KimJorgensen/KungFuFlash/firmware/d64.h

/*
 * Copyright (c) 2019-2023 Kim Jørgensen
 *
 * This software is provided 'as-is', without any express or implied
 * warranty.  In no event will the authors be held liable for any damages
 * arising from the use of this software.
 *
 * Permission is granted to anyone to use this software for any purpose,
 * including commercial applications, and to alter it and redistribute it
 * freely, subject to the following restrictions:
 *
 * 1. The origin of this software must not be misrepresented; you must not
 *    claim that you wrote the original software. If you use this software
 *    in a product, an acknowledgment in the product documentation would be
 *    appreciated but is not required.
 * 2. Altered source versions must be plainly marked as such, and must not be
 *    misrepresented as being the original software.
 * 3. This notice may not be removed or altered from any source distribution.
 *
 ******************************************************************************
 * Based on d642prg V2.09
 * Original source (C) Covert Bitops
 * (C)2003/2009 by iAN CooG/HokutoForce^TWT^HVSC
 */

#define D64_DOS_VERSION     0x41
#define D81_DOS_VERSION     0x44

#define D64_TRACKS          35
#define D71_TRACKS          70
#define D81_TRACKS          80
#define D81_SECTORS         40

#define D64_TRACK_DIR       18
#define D64_SECTOR_HEADER   0
#define D64_SECTOR_DIR      1
#define D81_TRACK_DIR       40
#define D81_SECTOR_DIR      3

#define D64_SECTOR_DATA_LEN 254
#define D64_SECTOR_LEN      256

static const u16 d64_track_offset[42] =
{
    0x0000, 0x0015, 0x002a, 0x003f, 0x0054, 0x0069, 0x007e, 0x0093,
    0x00a8, 0x00bd, 0x00d2, 0x00e7, 0x00fc, 0x0111, 0x0126, 0x013b,
    0x0150, 0x0165, 0x0178, 0x018b, 0x019e, 0x01b1, 0x01c4, 0x01d7,
    0x01ea, 0x01fc, 0x020e, 0x0220, 0x0232, 0x0244, 0x0256, 0x0267,
    0x0278, 0x0289, 0x029a, 0x02ab, 0x02bc, 0x02cd, 0x02de, 0x02ef,
    0x0300, 0x0311
};

static const char *d64_types[8] = {"DEL", "SEQ", "PRG", "USR", "REL", "CBM", "DIR", "???"};

typedef enum
{
  D64_TYPE_UNKNOWN = 0,
  D64_TYPE_D64,
  D64_TYPE_D71,
  D64_TYPE_D81
} D64_TYPE;

static u8 d64_get_type(FSIZE_t imgsize)
{
    switch (imgsize)
    {
        // D64
        case 174848:  // 35 tracks no errors
        case 175531:  // 35 w/ errors
        case 196608:  // 40 tracks no errors
        case 197376:  // 40 w/ errors
        case 205312:  // 42 tracks no errors
        case 206114:  // 42 w/ errors
            return D64_TYPE_D64;

        // D71
        case 349696:  // 70 tracks no errors
        case 351062:  // 70 w/ errors
            return D64_TYPE_D71;

        // D81
        case 819200:  // 80 tracks no errors
        case 822400:  // 80 w/ errors
            return D64_TYPE_D81;
    }

    return D64_TYPE_UNKNOWN;
}

typedef enum
{
  D64_FILE_DEL      = 0x00,
  D64_FILE_SEQ,
  D64_FILE_PRG,
  D64_FILE_USR,
  D64_FILE_REL,
  D64_FILE_CBM,
  D64_FILE_DIR,
  D64_FILE_LOCKED   = 0x40,
  D64_FILE_NO_SPLAT = 0x80
} D64_FILE_TYPE;

#pragma pack(push)
#pragma pack(1)
typedef struct
{
    u8 track;
    u8 sector;
} D64_TS;

typedef struct
{
    D64_TS current;                 // not persisted in D64
    D64_TS next;
    u8 data[D64_SECTOR_DATA_LEN];
} D64_SECTOR;

typedef struct
{
    u8 free_sectors;
    u8 data[3];
} D64_BAM_ENTRY;

typedef struct
{
    D64_TS current;
    D64_TS next;
    u8 dos_version;
    u8 double_sided;                // Only used by D71
    D64_BAM_ENTRY entries[35];
    char diskname[27];
    u8 unused;
    D64_BAM_ENTRY dolphin_dos[5];
    D64_BAM_ENTRY speed_dos[5];
    u8 unused2[9];
    u8 free_sectors_36_70[35];      // Only used by D71
} D64_HEADER_SECTOR;

typedef struct
{
    u8 data[3];
} D71_BAM_ENTRY;

typedef struct
{
    D64_TS current;
    D71_BAM_ENTRY entries[35];
    u8 unused[151];
} D71_BAM_SECTOR;

typedef struct
{
    u8 free_sectors;
    u8 data[5];
} D81_BAM_ENTRY;

typedef struct
{
    D64_TS current;
    D64_TS next;
    u16 version;
    u16 disk_id;
    u8 io_byte;
    u8 auto_boot;
    u8 reserved[8];
    D81_BAM_ENTRY entries[40];
} D81_BAM_SECTOR;

typedef struct
{
    D64_TS current;
    D64_TS next;
    u8 dos_version;
    u8 unused;
    char diskname[27];
    u8 unused2[225];
} D81_HEADER_SECTOR;

typedef struct
{
    D64_TS next;
    u8 type;            // D64_FILE_TYPE
    D64_TS start;
    char filename[16];
    u8 ignored[9];
    u16 blocks;
} D64_DIR_ENTRY;

typedef struct
{
    D64_TS current;
    D64_DIR_ENTRY entries[8];
} D64_DIR_SECTOR;
#pragma pack(pop)

typedef struct
{
    FIL file;
    u8 type;            // D64_TYPE

    union               // Cached header/BAM sectors
    {
        D64_SECTOR header;
        D64_HEADER_SECTOR d64_header;
        D81_HEADER_SECTOR d81_header;
    };
    union
    {
        D64_SECTOR bam;
        D71_BAM_SECTOR d71_bam;
        D81_BAM_SECTOR d81_bam1;
    };
    union
    {
        D64_SECTOR bam2;
        D81_BAM_SECTOR d81_bam2;
    };
} D64_IMAGE;

typedef struct
{
    D64_TS start;
    D64_TS dir;
    u8 dir_ptr;
} D64_FILE_CREATE;

typedef struct
{
    D64_IMAGE *image;

    union
    {
        D64_SECTOR sector;
        D64_DIR_SECTOR dir;
    };

    u8 data_len;
    u8 data_ptr;

    u8 sector_count;

    D64_FILE_CREATE file;
} D64;
